blak3r/treadspan/screenshots/ipad-screenshots/1242-1.jpg

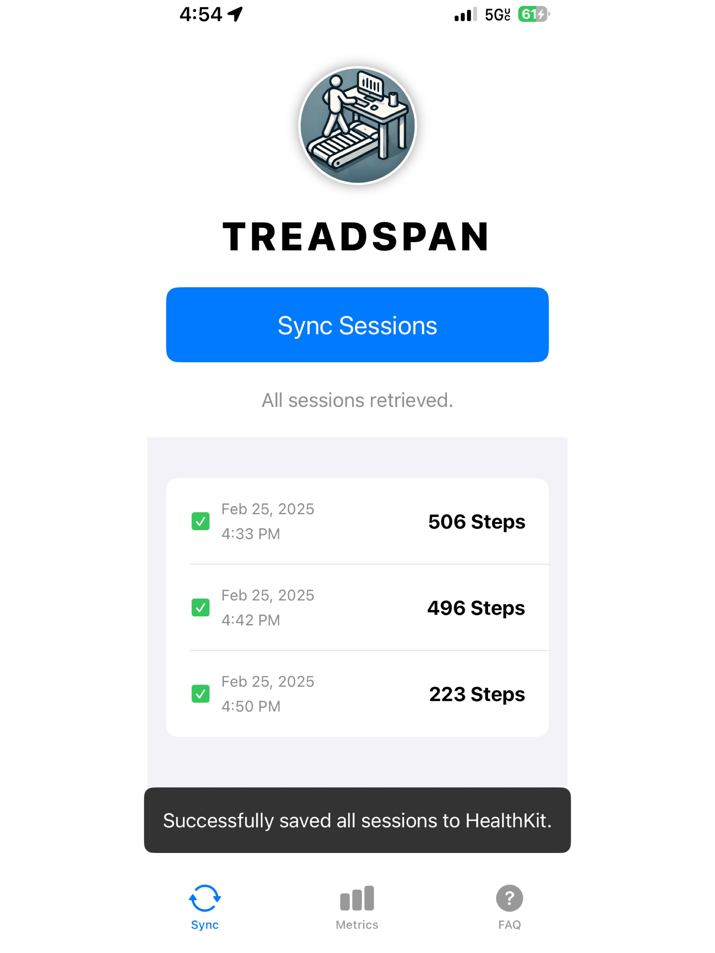
screenshots/ipad-screenshots/1242-1.jpg
