blak3r/treadspan/screenshots/ipad-screenshots/IMG_5388.jpg

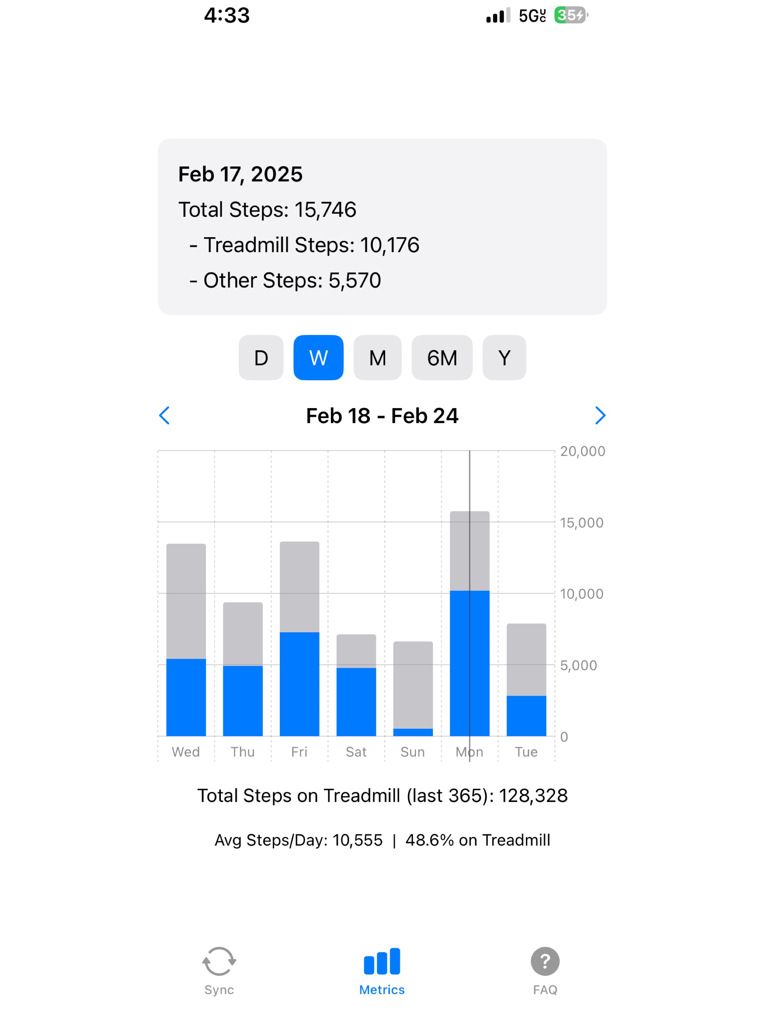
screenshots/ipad-screenshots/IMG_5388.jpg
