blak3r/treadspan/arduino/src/icons.h

// // array size is 32768
// static const uint16_t treadspan128[] PROGMEM  = {
//   0x0000, 0x0000, 0x0000, 0x0000, 0x0000, 0x0000, 0x0000, 0x0000, 0x0000, 0x0000, 0x0000, 0x0000, 0x0000, 0x0000, 0x0000, 0x0000, 0x0000, 0x0000, 0x0000, 0x0000, 0x0000, 0x9d34, 0xa596, 0xb617, 0xb618, 0xadf7, 0xadd7, 0xadf7, 0xae18, 0xb618, 0xae18, 0xb618, 0xadf8, 0xae18, 0xae18, 0xadf8, 0xadf8, 0xadf8, 0xadf8, 0xadf8, 0xadf8, 0xadf7, 0xadf7, 0xadf7, 0xadf8, 0xadf8, 0xadf7, 0xa5d7, 0xadd7, 0xadd7, 0xadd7, 0xa5d7, 0xa5b7, 0xa5b7, 0xa5d7, 0xa5d7, 0xa5d7, 0xa5d7, 0xadf7, 0xadf8, 0xadf8, 0xadf8, 0xadf7, 0xadf7, 0xa5f8, 0xa5f7, 0xa5f7, 0xadf8, 0xa5f8, 0xa5d7, 0xa5f8, 0xadf8, 0xa5d8, 0xa5d8, 0xa5d7, 0xa5d7, 0xa5d7, 0xa5d7, 0xa5d7, 0xa5d7, 0xadf7, 0xadf7, 0xadd7, 0xa5d7, 0xa5b7, 0x9db7, 0x9d96, 0x9d96, 0x9d96, 0x9d96, 0x9d97, 0x9d96, 0x9d96, 0x9d96, 0x9d76, 0x9576, 0x9d76, 0x9d76, 0x9d76, 0x9d76, 0x9576, 0x9555, 0x9d76, 0x9d96, 0xa596, 0x9d55, 0x7bef, 0x0000, 0x0000, 0x0000, 0x0000, 0x0000, 0x0000, 0x0000, 0x0000, 0x0000, 0x0000, 0x0000, 0x0000, 0x0000, 0x0000, 0x0000, 0x0000, 0x0000, 0x0000, 0x0000, 0x0000, 0x0000, 
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
//   0x7472, 0x6c52, 0x6c52, 0x6c32, 0x6431, 0x6431, 0x6431, 0x430d, 0x1966, 0x1125, 0x73ef, 0xdefa, 0xffde, 0xdefb, 0x73cf, 0x0905, 0x08c4, 0x29a7, 0xdefb, 0xffde, 0xb595, 0x29c7, 0x3209, 0xbdf7, 0xffde, 0xd6ba, 0x5aec, 0x1105, 0x7c10, 0xef7d, 0xf7be, 0x94f3, 0x1966, 0x426a, 0x8472, 0x1966, 0x3208, 0xa574, 0xdefa, 0x73cf, 0x1166, 0x3209, 0x08e4, 0x08c4, 0xa533, 0xffde, 0x8d14, 0x7431, 0x10e4, 0x534e, 0x5baf, 0x5bd0, 0x5bd0, 0x538f, 0x0905, 0xdefa, 0xffbd, 0x636e, 0x21e9, 0x53d0, 0x53b0, 0x53af, 0x538f, 0x536f, 
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
// };
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
