blak3r/treadspan/arduino/src/AGENCYB22pt7b.h

const uint8_t AGENCYB22pt7bBitmaps[] PROGMEM = {
  0x00, 0xFF, 0xFF, 0xFF, 0xFF, 0xFF, 0xFF, 0xFF, 0xFF, 0xFF, 0xFF, 0xFF,
  0xFF, 0xFF, 0xFF, 0xFF, 0x78, 0x00, 0x0F, 0xFF, 0xFF, 0xF8, 0xF9, 0xFF,
  0x9F, 0xF9, 0xFF, 0x9F, 0xF9, 0xF7, 0x0E, 0x70, 0xE7, 0x0E, 0x70, 0xE7,
  0x0E, 0x01, 0xE1, 0xE0, 0x0F, 0x0F, 0x00, 0x78, 0x78, 0x07, 0x87, 0x80,
  0x3C, 0x3C, 0x01, 0xE1, 0xE0, 0x0F, 0x0F, 0x00, 0x78, 0x78, 0x7F, 0xFF,
  0xFB, 0xFF, 0xFF, 0xDF, 0xFF, 0xFE, 0xFF, 0xFF, 0xF0, 0x78, 0x78, 0x03,
  0xC3, 0xC0, 0x1E, 0x1E, 0x00, 0xF0, 0xF0, 0x0F, 0x0F, 0x00, 0x78, 0x78,
  0x03, 0xC3, 0xC0, 0x1E, 0x1E, 0x00, 0xF0, 0xF0, 0x7F, 0xFF, 0xFB, 0xFF,
  0xFF, 0xDF, 0xFF, 0xFE, 0xFF, 0xFF, 0xF0, 0xF0, 0xF0, 0x07, 0x87, 0x80,
  0x3C, 0x3C, 0x01, 0xE1, 0xE0, 0x0F, 0x0F, 0x00, 0xF0, 0xF0, 0x07, 0x87,
  0x80, 0x3C, 0x3C, 0x00, 0x07, 0xC0, 0x0F, 0x80, 0x1F, 0x03, 0xFF, 0xEF,
  0xFF, 0xFF, 0xFF, 0xFF, 0xFF, 0xFF, 0xFF, 0xF8, 0x3F, 0xF0, 0x7F, 0xE0,
  0xFF, 0xC1, 0xFF, 0x83, 0xFF, 0x00, 0x3F, 0x00, 0x3F, 0x00, 0x3F, 0x00,
  0x3F, 0x00, 0x3F, 0x00, 0x3F, 0x00, 0x3E, 0x00, 0x3E, 0x00, 0x7E, 0x00,
  0x7E, 0x00, 0x7F, 0xF0, 0x7F, 0xE0, 0xFF, 0xC1, 0xFF, 0x83, 0xFF, 0x07,
  0xFE, 0x0F, 0xFF, 0xFF, 0xFF, 0xFF, 0xFF, 0xFF, 0xFF, 0xFB, 0xFF, 0xE0,
  0x7C, 0x00, 0xF8, 0x01, 0xF0, 0x00, 0x7F, 0x80, 0x1C, 0x7F, 0xE0, 0x1E,
  0x3F, 0xF0, 0x0E, 0x1C, 0x38, 0x0F, 0x0E, 0x1C, 0x07, 0x07, 0x0E, 0x07,
  0x83, 0x87, 0x03, 0x81, 0xC3, 0x83, 0xC0, 0xE1, 0xC1, 0xC0, 0x70, 0xE1,
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
  {  1897,  14,  33,  16,    2,  -32 },   // 0x46 'F'
  {  1955,  17,  33,  20,    2,  -32 },   // 0x47 'G'
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

const GFXfont AGENCYB22pt7b PROGMEM = {
  (uint8_t  *)AGENCYB22pt7bBitmaps,
  (GFXglyph *)AGENCYB22pt7bGlyphs,
  0x20, 0x7E, 52 };

// Approx. 5530 bytes
